croningp/BZComputation/hardware/CAD_Designs/pngs/1D_bottom.png

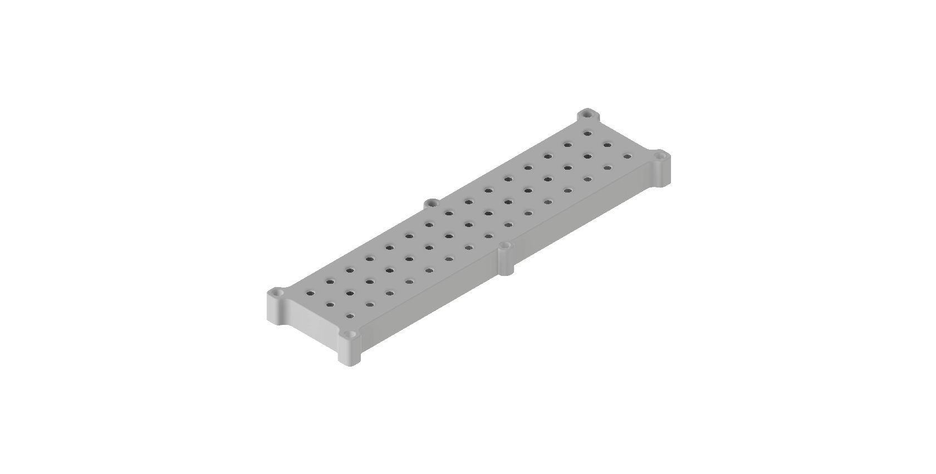
hardware/CAD_Designs/pngs/1D_bottom.png
