croningp/BZComputation/hardware/CAD_Designs/pngs/2D_bottom.png

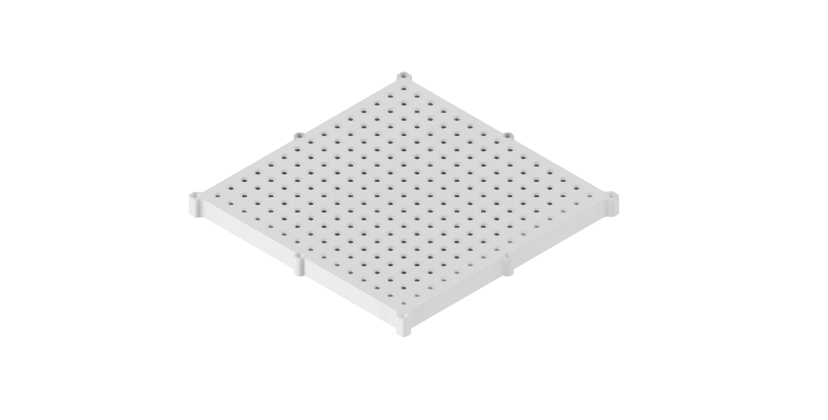
hardware/CAD_Designs/pngs/2D_bottom.png
