croningp/BZComputation/hardware/CAD_Designs/pngs/moto_magnets.png

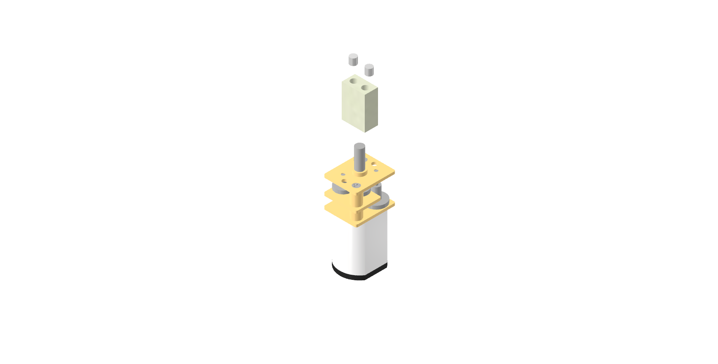
hardware/CAD_Designs/pngs/moto_magnets.png
